asicdruide/CMPG/Portal/1x_5mm_Portal-motor_spacer.dxf

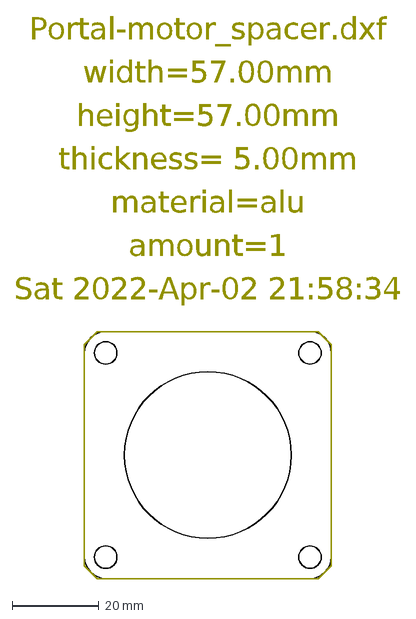
[picture p15: CAD file, 2022-04-06]
Portal/1x_5mm_Portal-motor_spacer.dxf
Portal-motor_spacer.dxf
width=57.00mm
height=57.00mm
thickness= 5.00mm
material=alu
amount=1
Sat 2022-Apr-02 21:58:34
