asicdruide/CMPG/Z-Axis/1x_15mm_Z-Axis-top.dxf

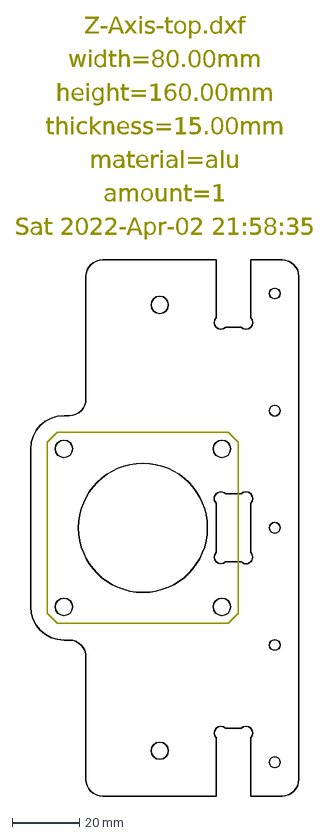
[picture p16: CAD file, 2022-04-06]
Z-Axis/1x_15mm_Z-Axis-top.dxf
Z-Axis-top.dxf
width=80.00mm
height=160.00mm
thickness=15.00mm
material=alu
amount=1
Sat 2022-Apr-02 21:58:35
