asicdruide/CMPG/Frame/1x_10mm_Frame-back-left.dxf

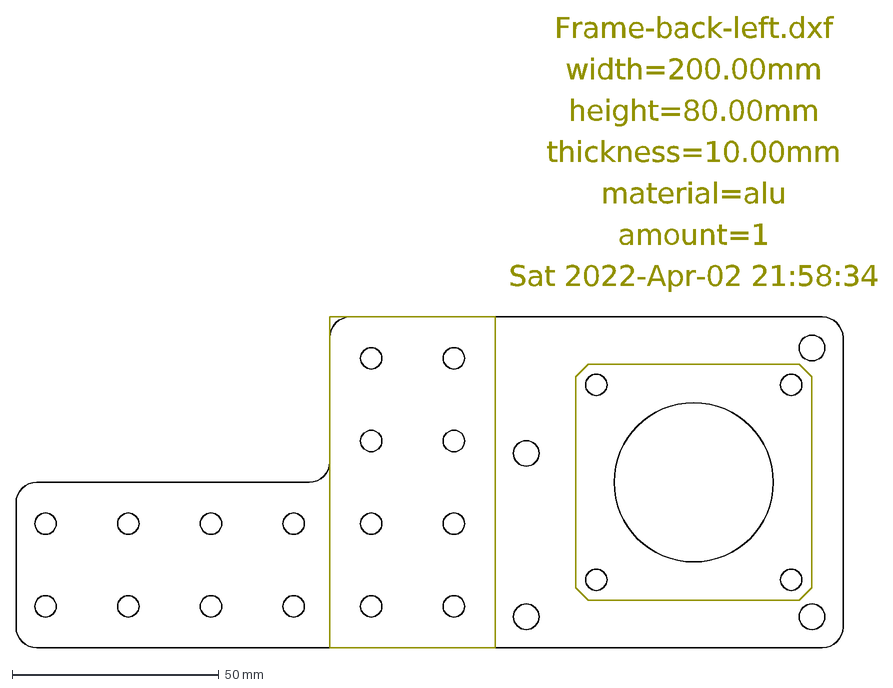
[picture p17: CAD file, 2022-04-06]
Frame/1x_10mm_Frame-back-left.dxf
Frame-back-left.dxf
width=200.00mm
height=80.00mm
thickness=10.00mm
material=alu
amount=1
Sat 2022-Apr-02 21:58:34
