asicdruide/CMPG/generated/1x_5mm_Portal-motor_spacer.dxf

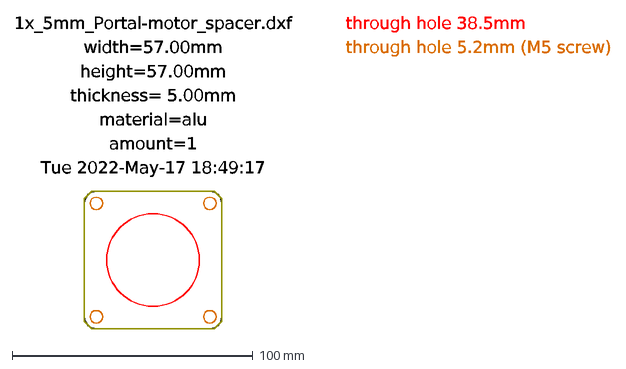
[picture p18: CAD file, 2022-05-19]
generated/1x_5mm_Portal-motor_spacer.dxf
1x_5mm_Portal-motor_spacer.dxf
width=57.00mm
height=57.00mm
thickness= 5.00mm
material=alu
amount=1
Tue 2022-May-17 18:49:17
through hole 38.5mm
through hole 5.2mm (M5 screw)
