asicdruide/CMPG/Z-Axis/1x_10mm_Z-Axis-spindle-AM_1.5kW_ER11.dxf

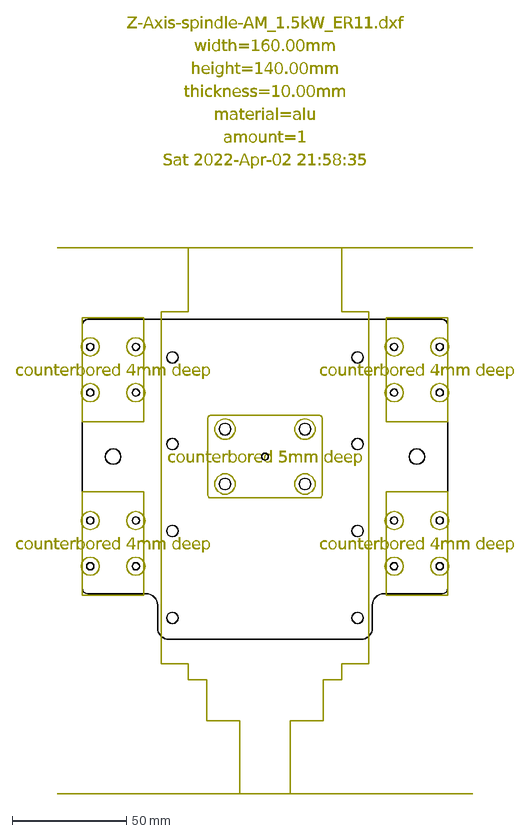
[picture p19: CAD file, 2022-04-06]
Z-Axis/1x_10mm_Z-Axis-spindle-AM_1.5kW_ER11.dxf
counterbored 4mm deep
counterbored 5mm deep
Z-Axis-spindle-AM_1.5kW_ER11.dxf
width=160.00mm
height=140.00mm
thickness=10.00mm
material=alu
amount=1
Sat 2022-Apr-02 21:58:35
