asicdruide/CMPG/generated/1x_10mm_Portal-block.dxf

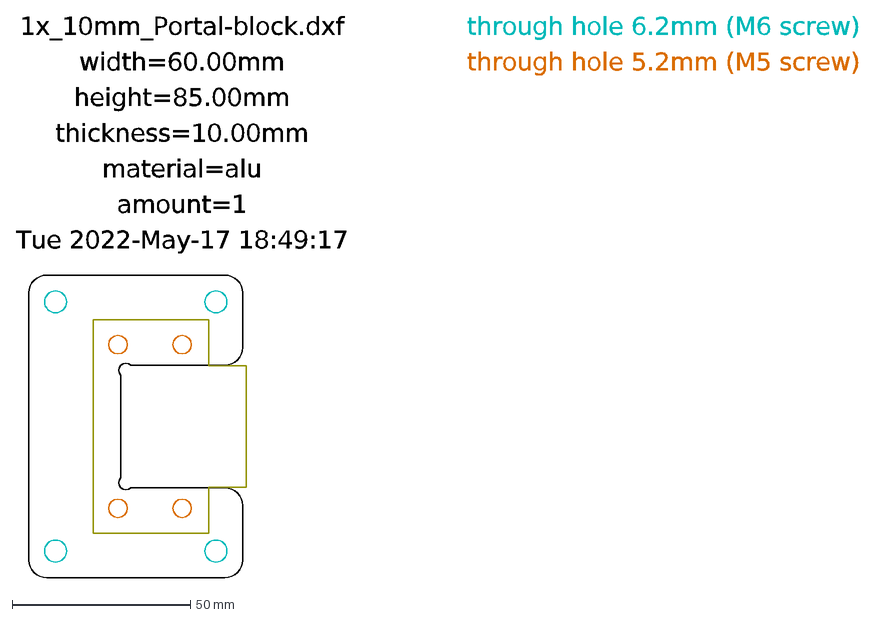
[picture p21: CAD file, 2022-05-19]
generated/1x_10mm_Portal-block.dxf
1x_10mm_Portal-block.dxf
width=60.00mm
height=85.00mm
thickness=10.00mm
material=alu
amount=1
Tue 2022-May-17 18:49:17
through hole 6.2mm (M6 screw)
through hole 5.2mm (M5 screw)
