asicdruide/CMPG/Portal/1x_10mm_Portal-motor_spacer.dxf

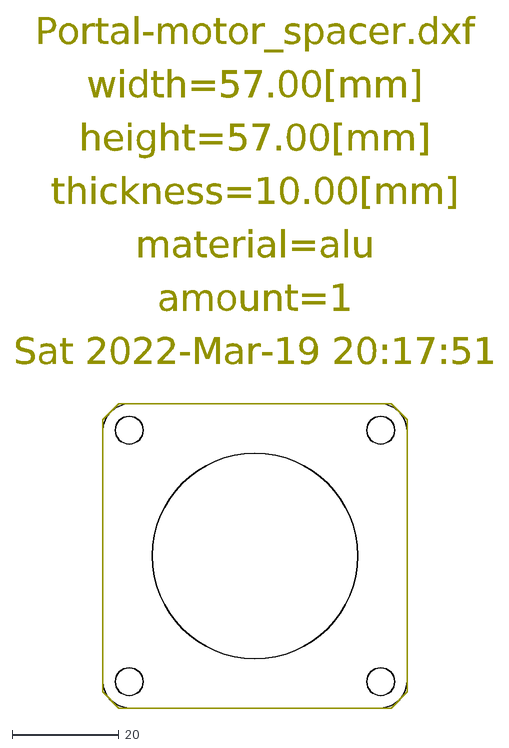
[picture p22: CAD file, 2022-03-19]
Portal/1x_10mm_Portal-motor_spacer.dxf
Portal-motor_spacer.dxf
width=57.00[mm]
height=57.00[mm]
thickness=10.00[mm]
material=alu
amount=1
Sat 2022-Mar-19 20:17:51
