asicdruide/CMPG/Z-Axis/1x_10mm_Z-Axis-back.dxf

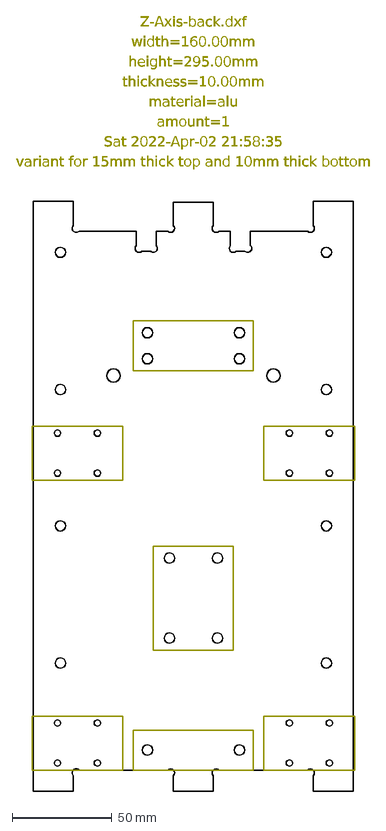
[picture p23: CAD file, 2022-04-06]
Z-Axis/1x_10mm_Z-Axis-back.dxf
Z-Axis-back.dxf
width=160.00mm
height=295.00mm
thickness=10.00mm
material=alu
amount=1
Sat 2022-Apr-02 21:58:35
variant for 15mm thick top and 10mm thick bottom
