asicdruide/CMPG/Frame/1x_10mm_Frame-Plate-back-left.dxf

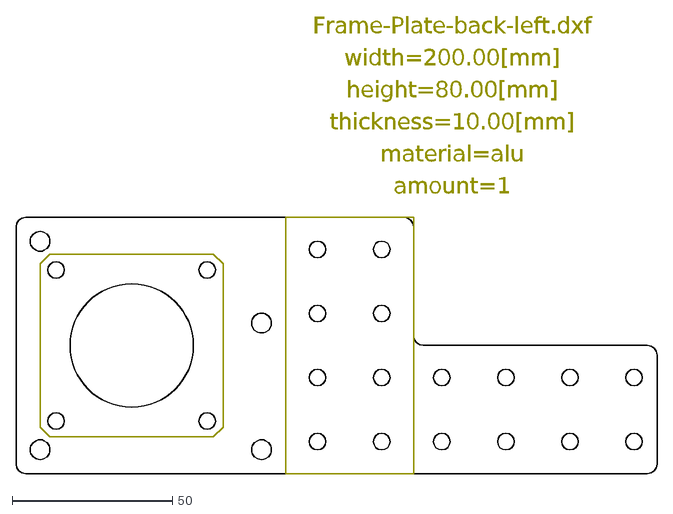
[picture p24: CAD file, 2022-03-18]
Frame/1x_10mm_Frame-Plate-back-left.dxf
Frame-Plate-back-left.dxf
width=200.00[mm]
height=80.00[mm]
thickness=10.00[mm]
material=alu
amount=1
