asicdruide/CMPG/generated/1x_10mm_ZAxis-bottom.dxf

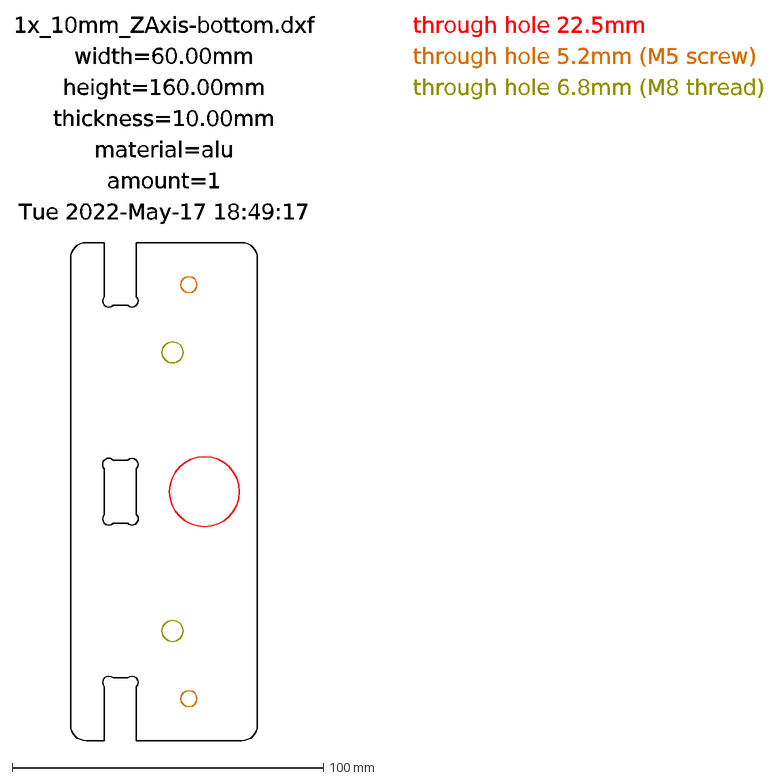
[picture p25: CAD file, 2022-05-19]
generated/1x_10mm_ZAxis-bottom.dxf
1x_10mm_ZAxis-bottom.dxf
width=60.00mm
height=160.00mm
thickness=10.00mm
material=alu
amount=1
Tue 2022-May-17 18:49:17
through hole 22.5mm
through hole 5.2mm (M5 screw)
through hole 6.8mm (M8 thread)
