asicdruide/CMPG/Portal/2x_5mm_Portal-side_plate_spacer.dxf

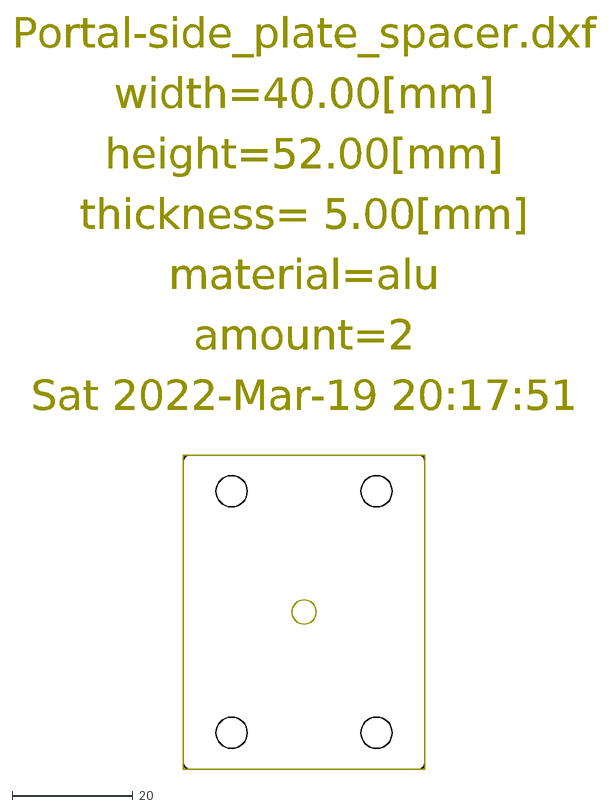
[picture p26: CAD file, 2022-03-19]
Portal/2x_5mm_Portal-side_plate_spacer.dxf
Portal-side_plate_spacer.dxf
width=40.00[mm]
height=52.00[mm]
thickness= 5.00[mm]
material=alu
amount=2
Sat 2022-Mar-19 20:17:51
