asicdruide/CMPG/Portal/1x_10mm_Portal-side-left.dxf

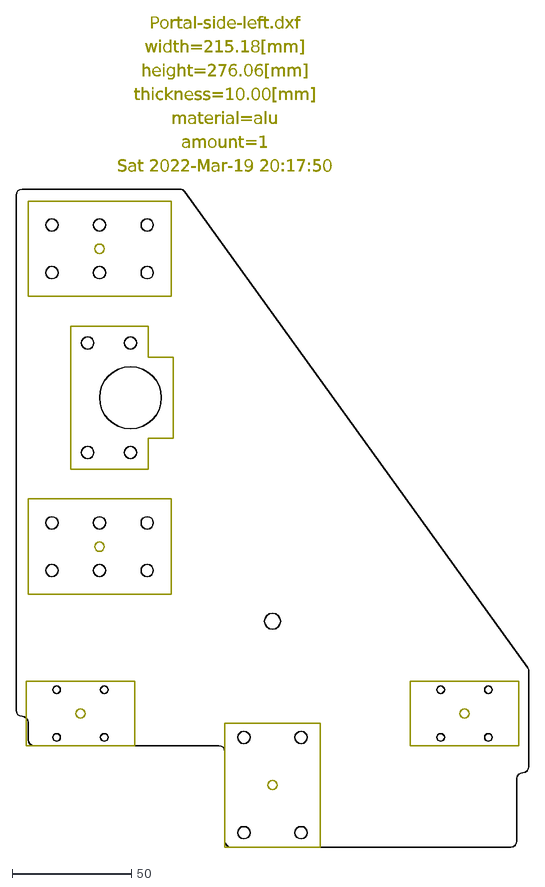
[picture p30: CAD file, 2022-03-19]
Portal/1x_10mm_Portal-side-left.dxf
Portal-side-left.dxf
width=215.18[mm]
height=276.06[mm]
thickness=10.00[mm]
material=alu
amount=1
Sat 2022-Mar-19 20:17:50
