asicdruide/CMPG/Z-Axis/1x_10mm_Z-Axis-spindle-GP_2.2kW_ER20.dxf

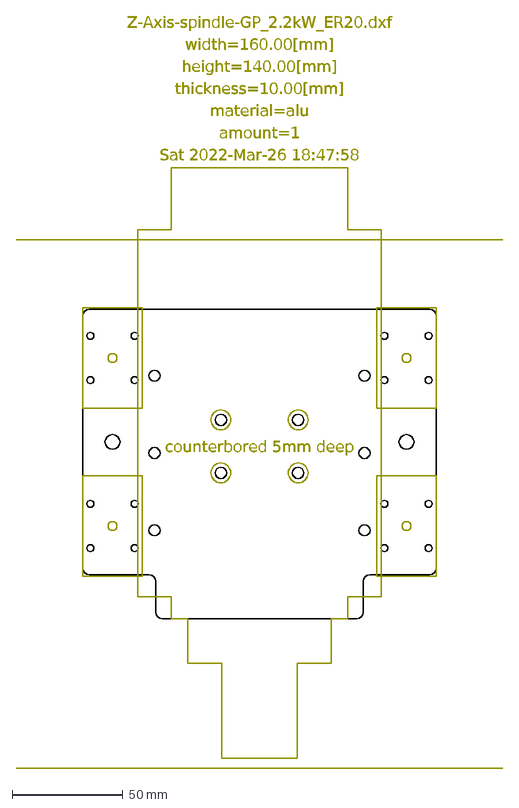
[picture p31: CAD file, 2022-03-27]
Z-Axis/1x_10mm_Z-Axis-spindle-GP_2.2kW_ER20.dxf
counterbored 5mm deep
Z-Axis-spindle-GP_2.2kW_ER20.dxf
width=160.00[mm]
height=140.00[mm]
thickness=10.00[mm]
material=alu
amount=1
Sat 2022-Mar-26 18:47:58
