asicdruide/CMPG/Frame/1x_10mm_Frame-Plate-block-right.dxf

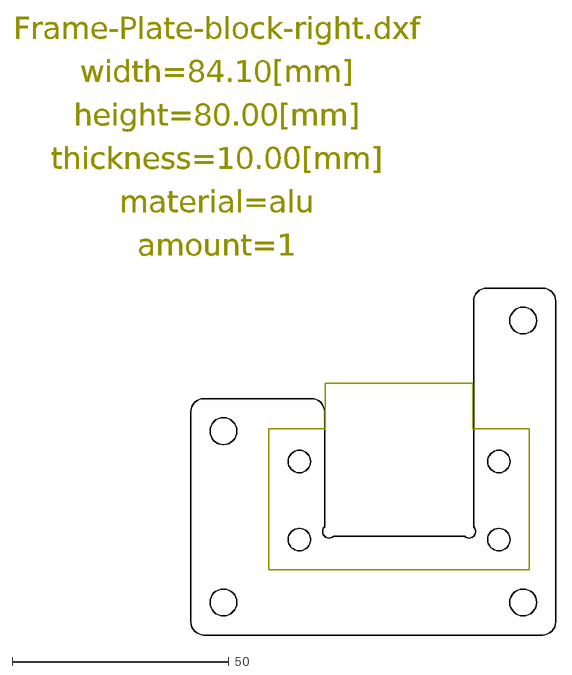
[picture p32: CAD file, 2022-03-18]
Frame/1x_10mm_Frame-Plate-block-right.dxf
Frame-Plate-block-right.dxf
width=84.10[mm]
height=80.00[mm]
thickness=10.00[mm]
material=alu
amount=1
