asicdruide/CMPG/generated/1x_10mm_Frame-front-left.dxf

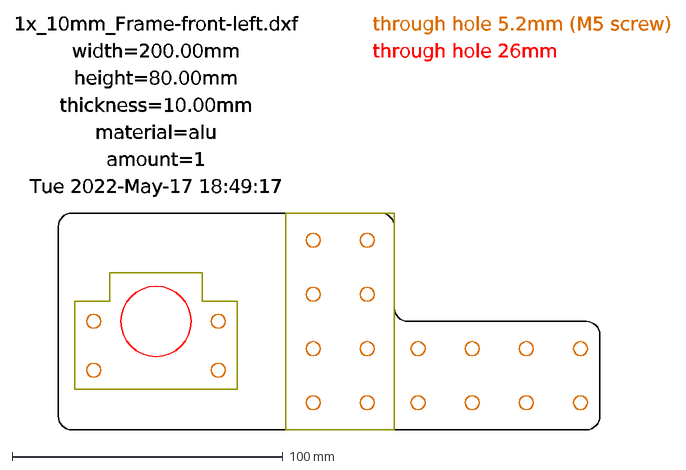
[picture p33: CAD file, 2022-05-19]
generated/1x_10mm_Frame-front-left.dxf
1x_10mm_Frame-front-left.dxf
width=200.00mm
height=80.00mm
thickness=10.00mm
material=alu
amount=1
Tue 2022-May-17 18:49:17
through hole 5.2mm (M5 screw)
through hole 26mm
