asicdruide/CMPG/Z-Axis/1x_5mm_Z-Axis-motor_spacer.dxf

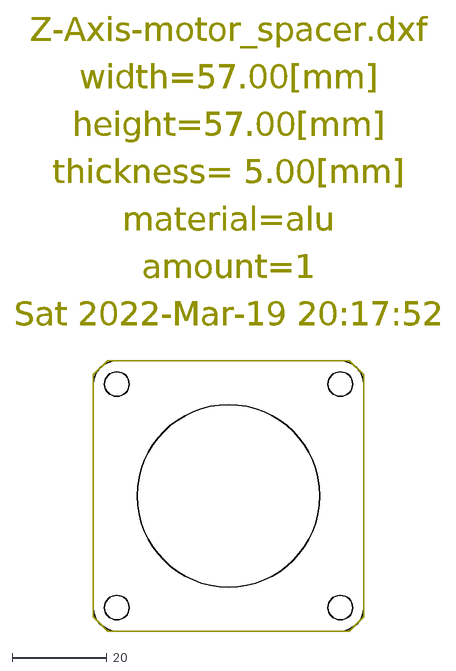
[picture p35: CAD file, 2022-03-19]
Z-Axis/1x_5mm_Z-Axis-motor_spacer.dxf
Z-Axis-motor_spacer.dxf
width=57.00[mm]
height=57.00[mm]
thickness= 5.00[mm]
material=alu
amount=1
Sat 2022-Mar-19 20:17:52
