asicdruide/CMPG/Frame/1x_10mm_Frame-Plate-back-right.dxf

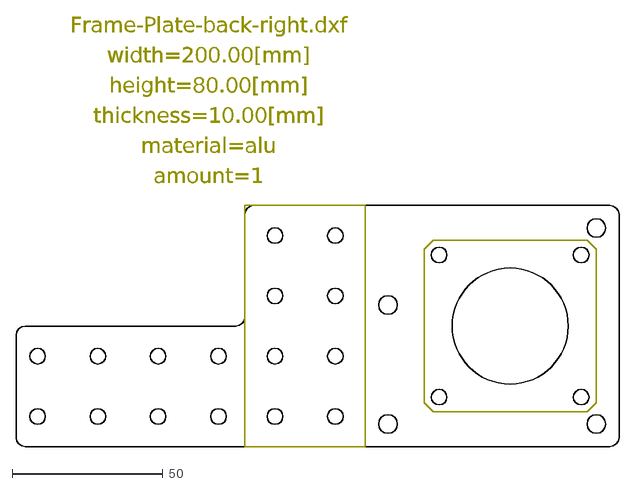
[picture p36: CAD file, 2022-03-18]
Frame/1x_10mm_Frame-Plate-back-right.dxf
Frame-Plate-back-right.dxf
width=200.00[mm]
height=80.00[mm]
thickness=10.00[mm]
material=alu
amount=1
