asicdruide/CMPG/Portal/1x_10mm_Portal-Plate-back.dxf

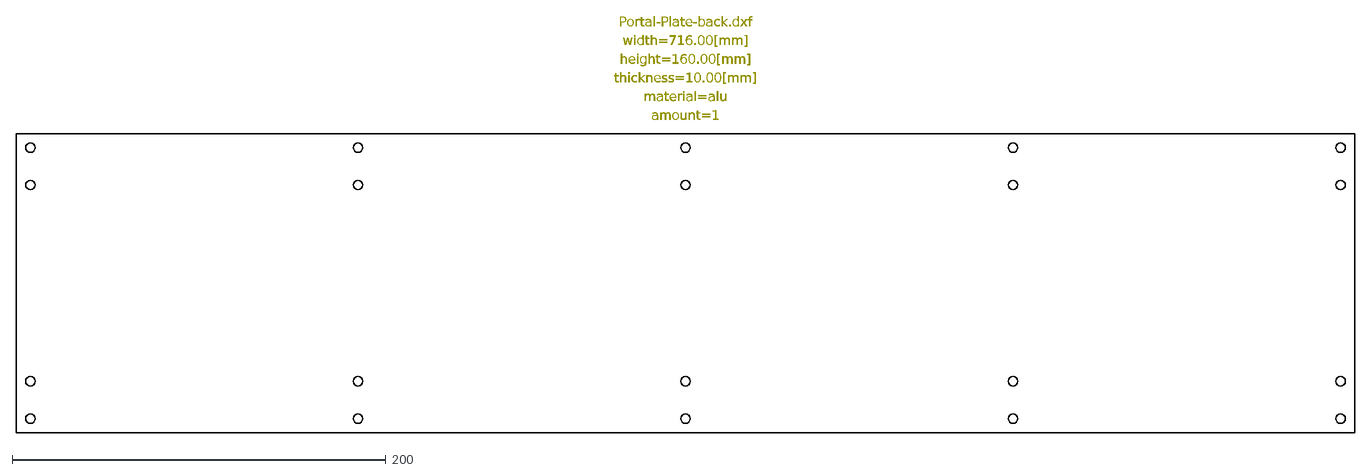
[picture p38: CAD file, 2022-03-18]
Portal/1x_10mm_Portal-Plate-back.dxf
Portal-Plate-back.dxf
width=716.00[mm]
height=160.00[mm]
thickness=10.00[mm]
material=alu
amount=1
