asicdruide/CMPG/Z-Axis/1x_10mm_Z-Axis-top.dxf

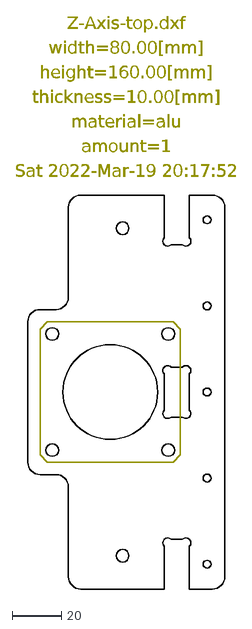
[picture p39: CAD file, 2022-03-19]
Z-Axis/1x_10mm_Z-Axis-top.dxf
Z-Axis-top.dxf
width=80.00[mm]
height=160.00[mm]
thickness=10.00[mm]
material=alu
amount=1
Sat 2022-Mar-19 20:17:52
