asicdruide/CMPG/Frame/1x_10mm_Frame-Plate-block-left.dxf

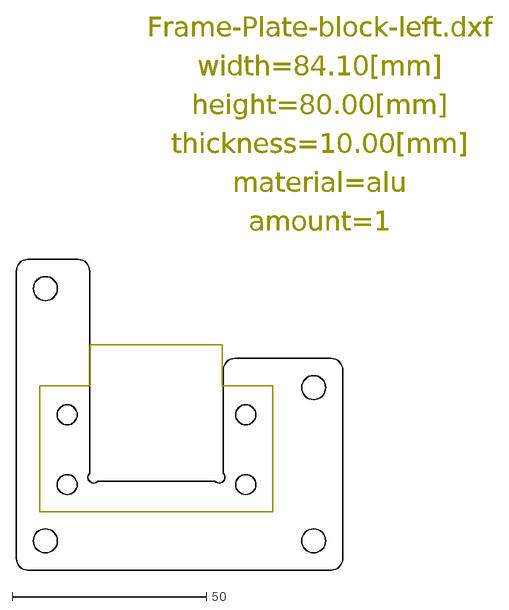
[picture p40: CAD file, 2022-03-18]
Frame/1x_10mm_Frame-Plate-block-left.dxf
Frame-Plate-block-left.dxf
width=84.10[mm]
height=80.00[mm]
thickness=10.00[mm]
material=alu
amount=1
