asicdruide/CMPG/generated/1x_15mm_Portal-side-left.dxf

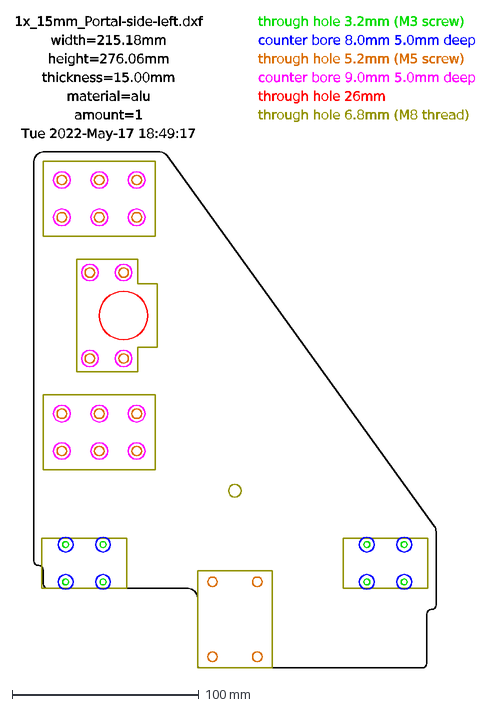
[picture p41: CAD file, 2022-05-19]
generated/1x_15mm_Portal-side-left.dxf
1x_15mm_Portal-side-left.dxf
width=215.18mm
height=276.06mm
thickness=15.00mm
material=alu
amount=1
Tue 2022-May-17 18:49:17
through hole 3.2mm (M3 screw)
counter bore 8.0mm 5.0mm deep
through hole 5.2mm (M5 screw)
counter bore 9.0mm 5.0mm deep
through hole 26mm
through hole 6.8mm (M8 thread)
