asicdruide/CMPG/Z-Axis/1x_10mm_Z-Axis-Plate-bottom.dxf

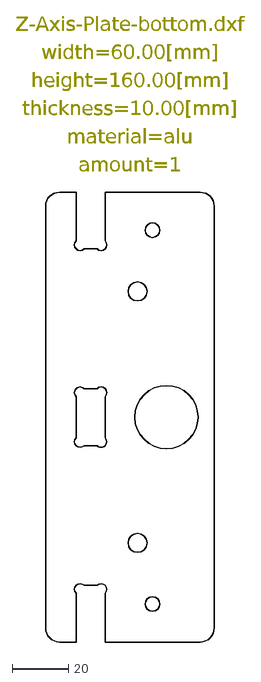
[picture p43: CAD file, 2022-03-18]
Z-Axis/1x_10mm_Z-Axis-Plate-bottom.dxf
Z-Axis-Plate-bottom.dxf
width=60.00[mm]
height=160.00[mm]
thickness=10.00[mm]
material=alu
amount=1
