asicdruide/CMPG/Frame/1x_10mm_Frame-Plate-front-left.dxf

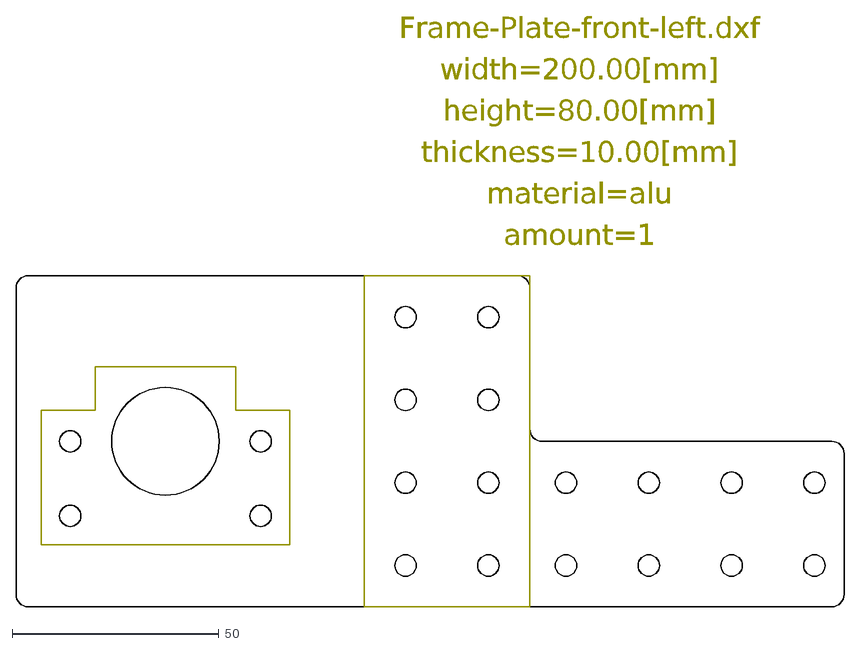
[picture p44: CAD file, 2022-03-18]
Frame/1x_10mm_Frame-Plate-front-left.dxf
Frame-Plate-front-left.dxf
width=200.00[mm]
height=80.00[mm]
thickness=10.00[mm]
material=alu
amount=1
