asicdruide/CMPG/generated/1x_15mm_ZAxis-top.dxf

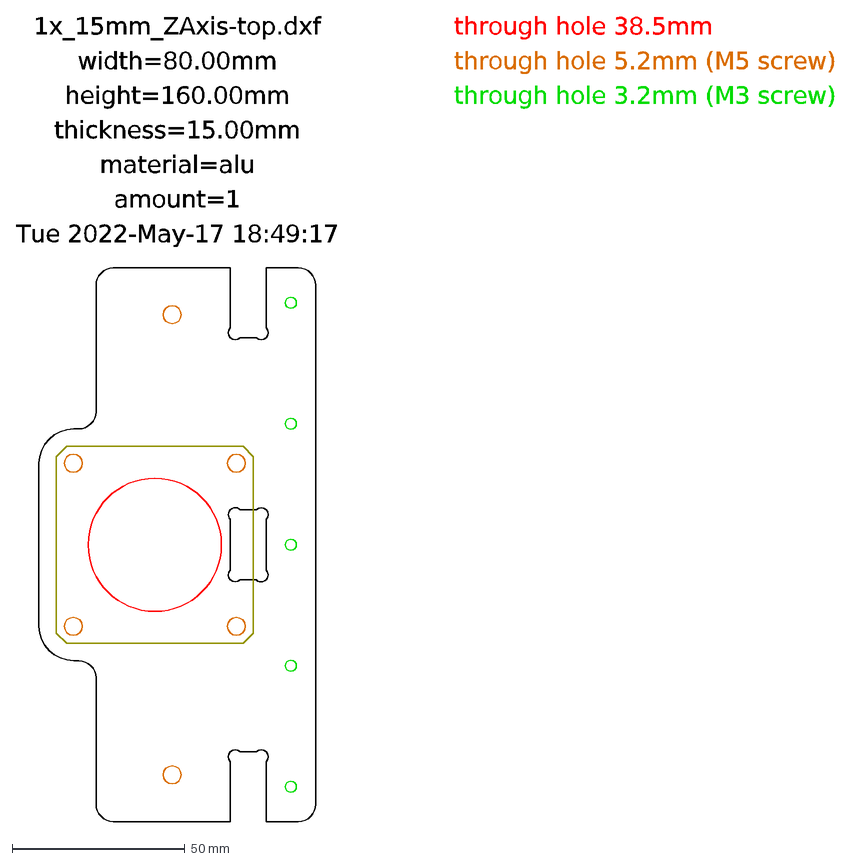
[picture p45: CAD file, 2022-05-19]
generated/1x_15mm_ZAxis-top.dxf
1x_15mm_ZAxis-top.dxf
width=80.00mm
height=160.00mm
thickness=15.00mm
material=alu
amount=1
Tue 2022-May-17 18:49:17
through hole 38.5mm
through hole 5.2mm (M5 screw)
through hole 3.2mm (M3 screw)
