asicdruide/CMPG/Portal/1x_10mm_Portal-Plate-side-right.dxf

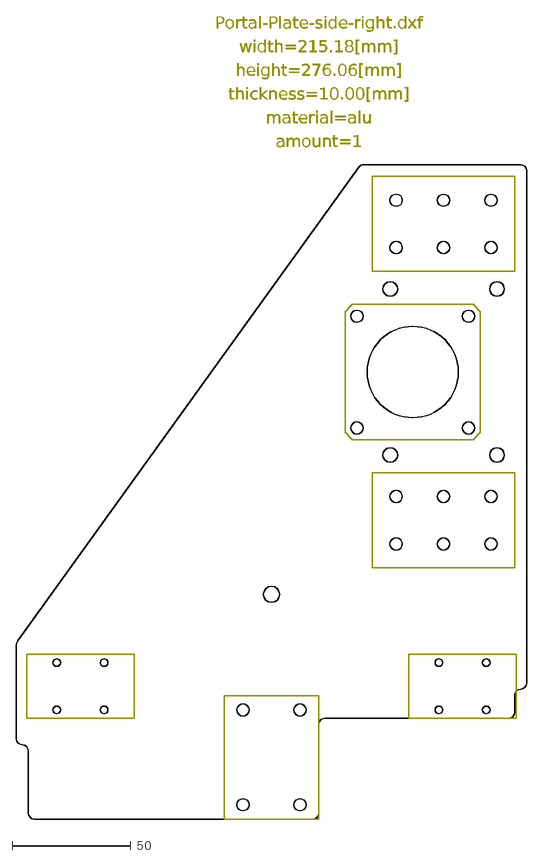
[picture p46: CAD file, 2022-03-18]
Portal/1x_10mm_Portal-Plate-side-right.dxf
Portal-Plate-side-right.dxf
width=215.18[mm]
height=276.06[mm]
thickness=10.00[mm]
material=alu
amount=1
