asicdruide/CMPG/Frame/Frame-Plate-front-right.dxf

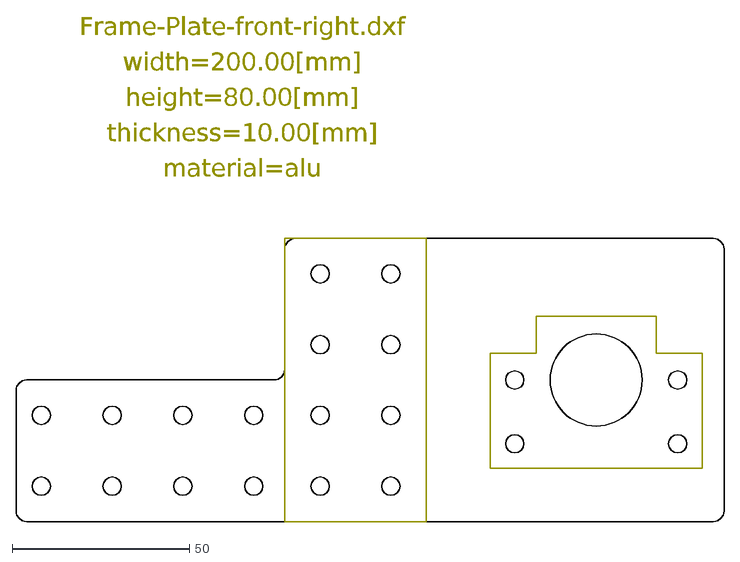
[picture p48: CAD file, 2022-03-16]
Frame/Frame-Plate-front-right.dxf
Frame-Plate-front-right.dxf
width=200.00[mm]
height=80.00[mm]
thickness=10.00[mm]
material=alu
