asicdruide/CMPG/generated/1x_10mm_Frame-back-right.dxf

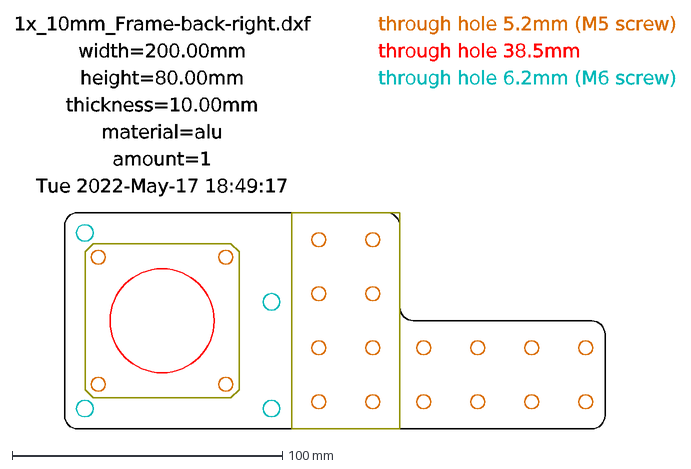
[picture p49: CAD file, 2022-05-19]
generated/1x_10mm_Frame-back-right.dxf
1x_10mm_Frame-back-right.dxf
width=200.00mm
height=80.00mm
thickness=10.00mm
material=alu
amount=1
Tue 2022-May-17 18:49:17
through hole 5.2mm (M5 screw)
through hole 38.5mm
through hole 6.2mm (M6 screw)
