asicdruide/CMPG/Portal/1x_10mm_Portal-Plate-block.dxf

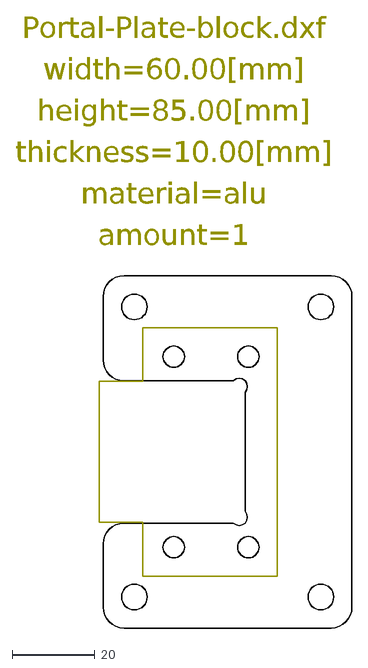
[picture p50: CAD file, 2022-03-18]
Portal/1x_10mm_Portal-Plate-block.dxf
Portal-Plate-block.dxf
width=60.00[mm]
height=85.00[mm]
thickness=10.00[mm]
material=alu
amount=1
