asicdruide/CMPG/Z-Axis/1x_10mm_Z-Axis-Spindle-Plate-GP_1.5kW_ER20.dxf

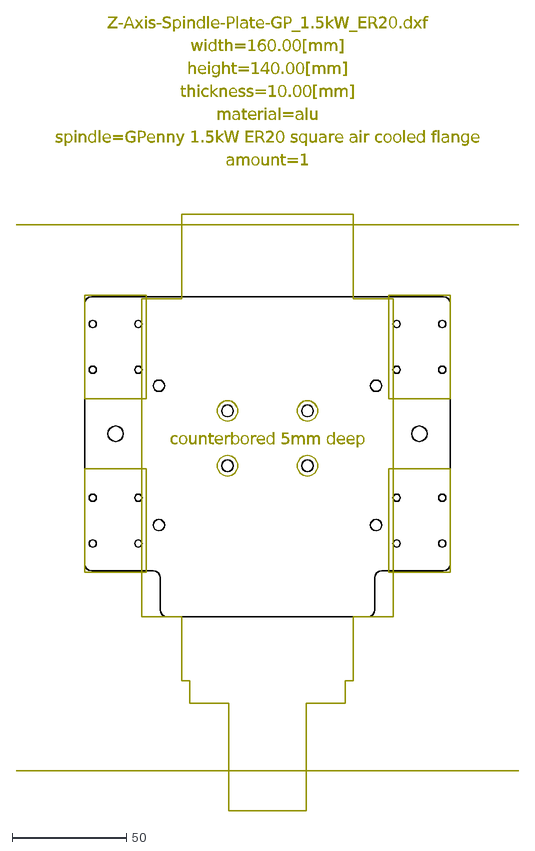
[picture p51: CAD file, 2022-03-18]
Z-Axis/1x_10mm_Z-Axis-Spindle-Plate-GP_1.5kW_ER20.dxf
counterbored 5mm deep
Z-Axis-Spindle-Plate-GP_1.5kW_ER20.dxf
width=160.00[mm]
height=140.00[mm]
thickness=10.00[mm]
material=alu
spindle=GPenny 1.5kW ER20 square air cooled flange
amount=1
