asicdruide/CMPG/Frame/Frame-Plate-back-right.dxf

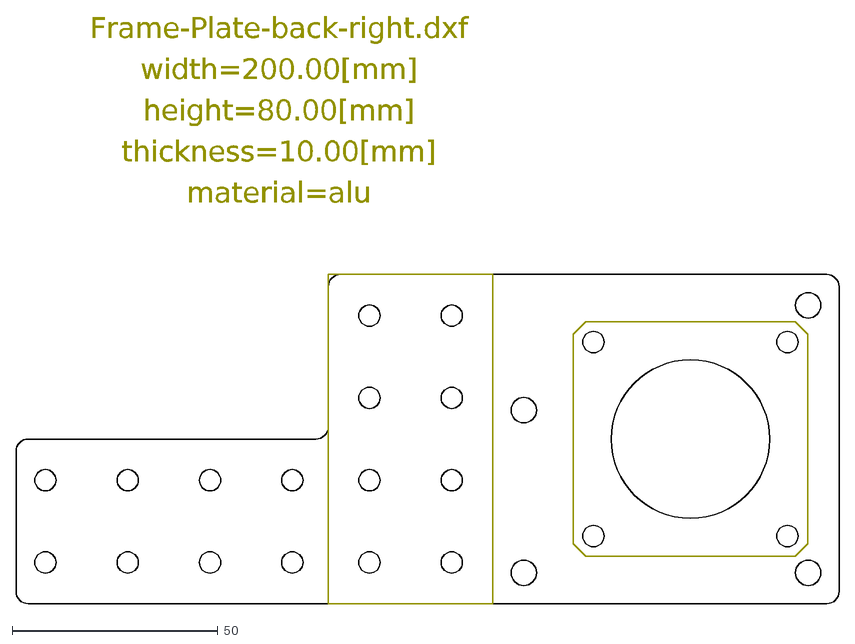
[picture p52: CAD file, 2022-03-16]
Frame/Frame-Plate-back-right.dxf
Frame-Plate-back-right.dxf
width=200.00[mm]
height=80.00[mm]
thickness=10.00[mm]
material=alu
