asicdruide/CMPG/Z-Axis/1x_10mm_Z-Axis-Spindle-Plate-AM_1.5kW_ER11.dxf

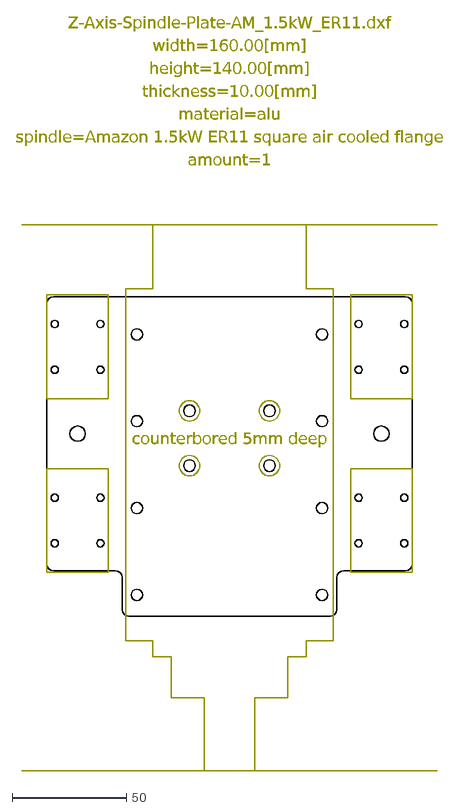
[picture p54: CAD file, 2022-03-18]
Z-Axis/1x_10mm_Z-Axis-Spindle-Plate-AM_1.5kW_ER11.dxf
counterbored 5mm deep
Z-Axis-Spindle-Plate-AM_1.5kW_ER11.dxf
width=160.00[mm]
height=140.00[mm]
thickness=10.00[mm]
material=alu
spindle=Amazon 1.5kW ER11 square air cooled flange
amount=1
