asicdruide/CMPG/Frame/Frame-Plate-front-left.dxf

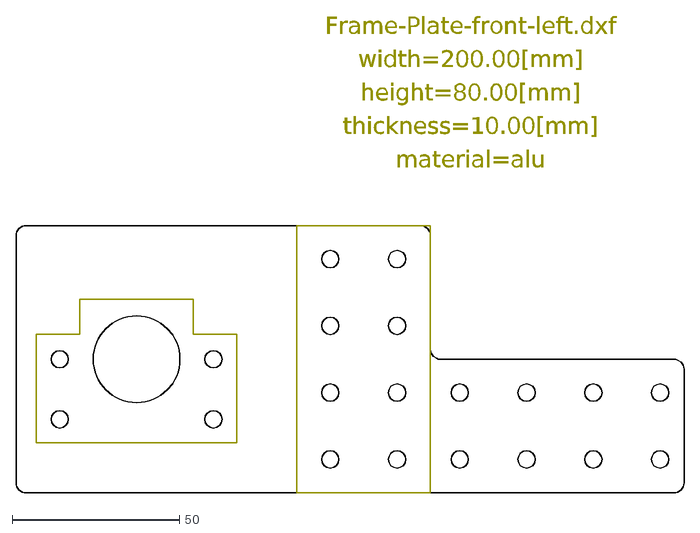
[picture p55: CAD file, 2022-03-16]
Frame/Frame-Plate-front-left.dxf
Frame-Plate-front-left.dxf
width=200.00[mm]
height=80.00[mm]
thickness=10.00[mm]
material=alu
