asicdruide/CMPG/Portal/1x_10mm_Portal-Plate-motor_spacer.dxf

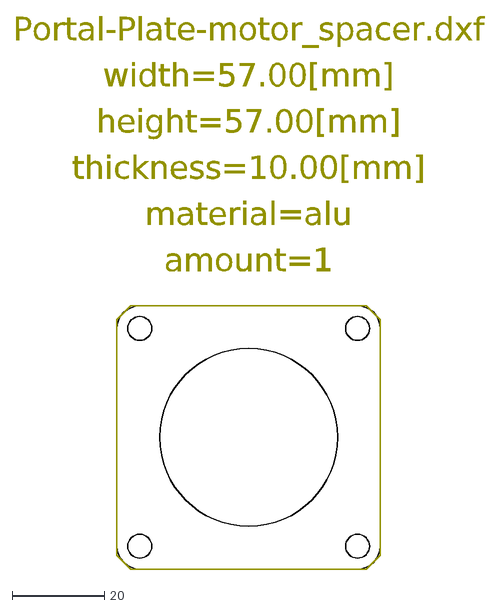
[picture p56: CAD file, 2022-03-18]
Portal/1x_10mm_Portal-Plate-motor_spacer.dxf
Portal-Plate-motor_spacer.dxf
width=57.00[mm]
height=57.00[mm]
thickness=10.00[mm]
material=alu
amount=1
