asicdruide/CMPG/Z-Axis/1x_10mm_Z-Axis-Plate-top.dxf

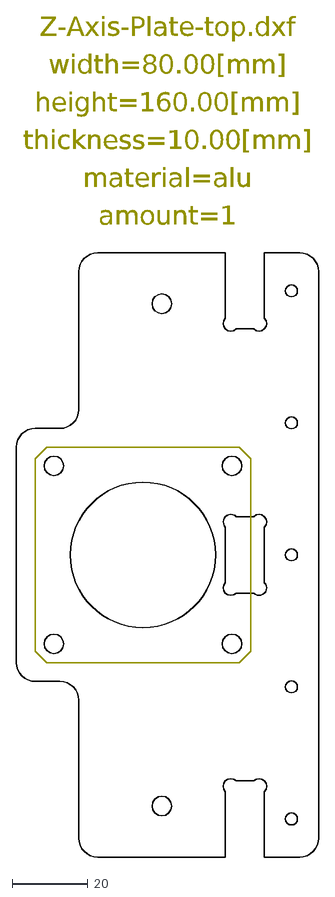
[picture p57: CAD file, 2022-03-18]
Z-Axis/1x_10mm_Z-Axis-Plate-top.dxf
Z-Axis-Plate-top.dxf
width=80.00[mm]
height=160.00[mm]
thickness=10.00[mm]
material=alu
amount=1
