asicdruide/CMPG/Frame/Frame-Plate-block-right.dxf

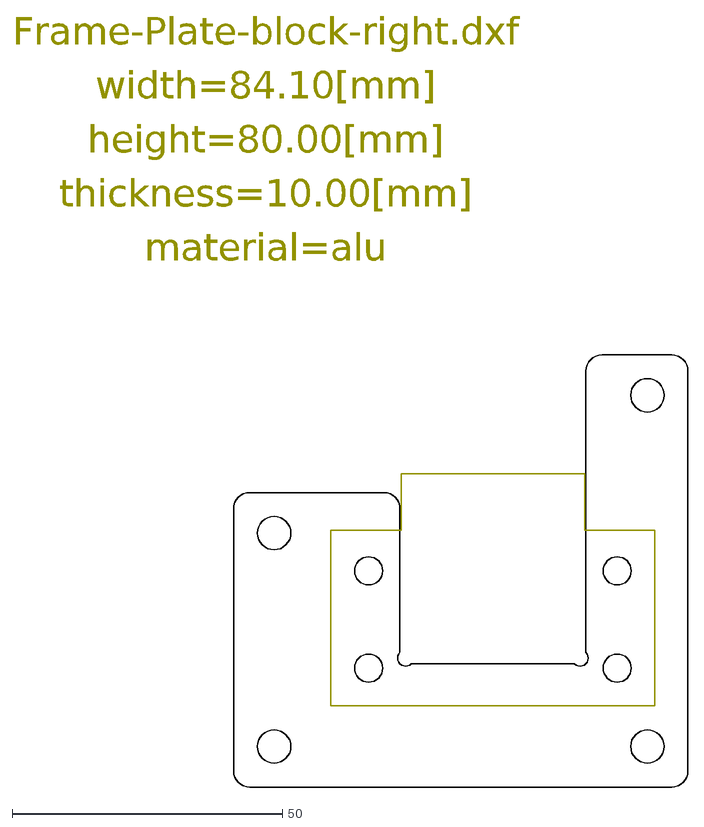
[picture p58: CAD file, 2022-03-16]
Frame/Frame-Plate-block-right.dxf
Frame-Plate-block-right.dxf
width=84.10[mm]
height=80.00[mm]
thickness=10.00[mm]
material=alu
