asicdruide/CMPG/generated/4x_7mm_ZAxis-rail_spacer.dxf

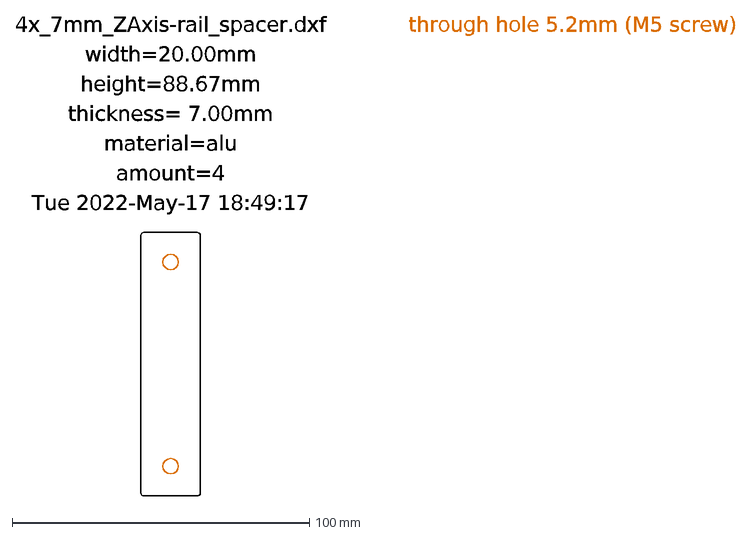
[picture p59: CAD file, 2022-05-19]
generated/4x_7mm_ZAxis-rail_spacer.dxf
4x_7mm_ZAxis-rail_spacer.dxf
width=20.00mm
height=88.67mm
thickness= 7.00mm
material=alu
amount=4
Tue 2022-May-17 18:49:17
through hole 5.2mm (M5 screw)
