asicdruide/CMPG/Portal/2x_5mm_Portal-Plate-side_plate_spacer.dxf

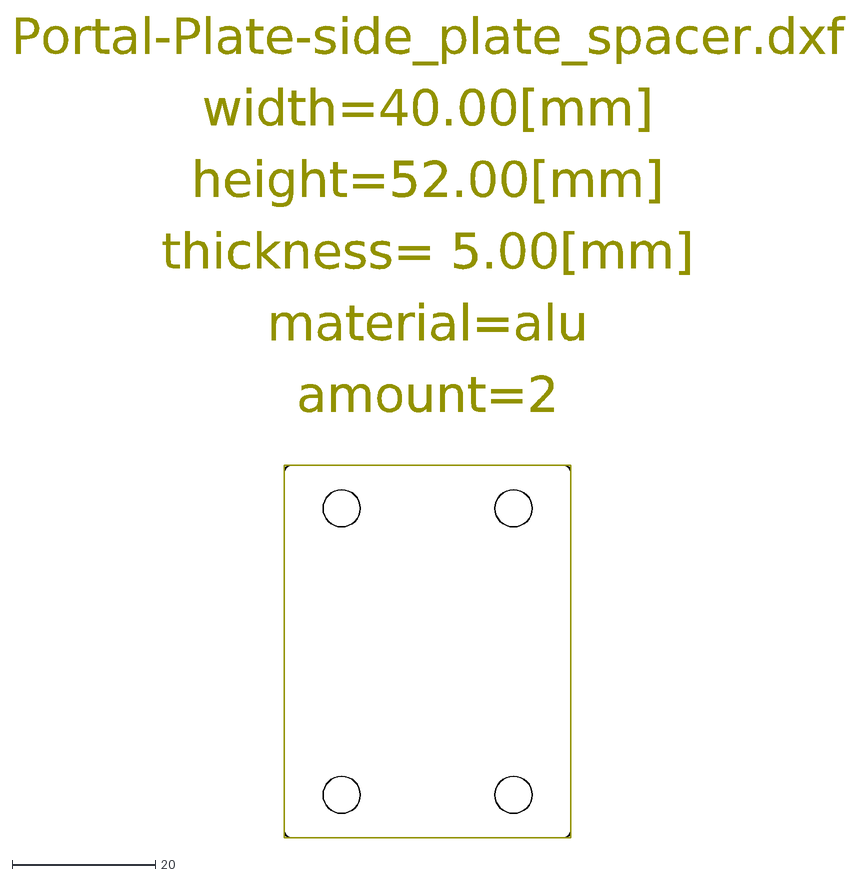
[picture p60: CAD file, 2022-03-18]
Portal/2x_5mm_Portal-Plate-side_plate_spacer.dxf
Portal-Plate-side_plate_spacer.dxf
width=40.00[mm]
height=52.00[mm]
thickness= 5.00[mm]
material=alu
amount=2
