asicdruide/CMPG/Z-Axis/1x_10mm_Z-Axis-Spindle-Plate-GP_2.2kW_ER20.dxf

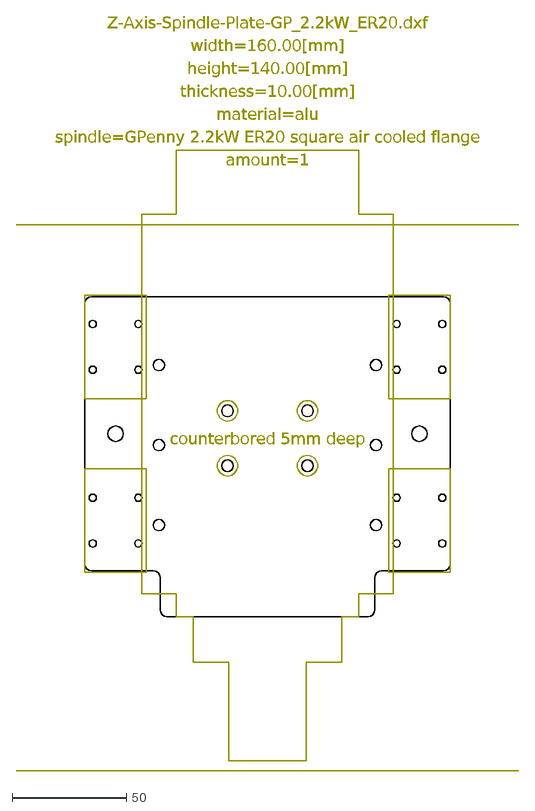
[picture p61: CAD file, 2022-03-18]
Z-Axis/1x_10mm_Z-Axis-Spindle-Plate-GP_2.2kW_ER20.dxf
counterbored 5mm deep
Z-Axis-Spindle-Plate-GP_2.2kW_ER20.dxf
width=160.00[mm]
height=140.00[mm]
thickness=10.00[mm]
material=alu
spindle=GPenny 2.2kW ER20 square air cooled flange
amount=1
