asicdruide/CMPG/Frame/Frame-Plate-back-left.dxf

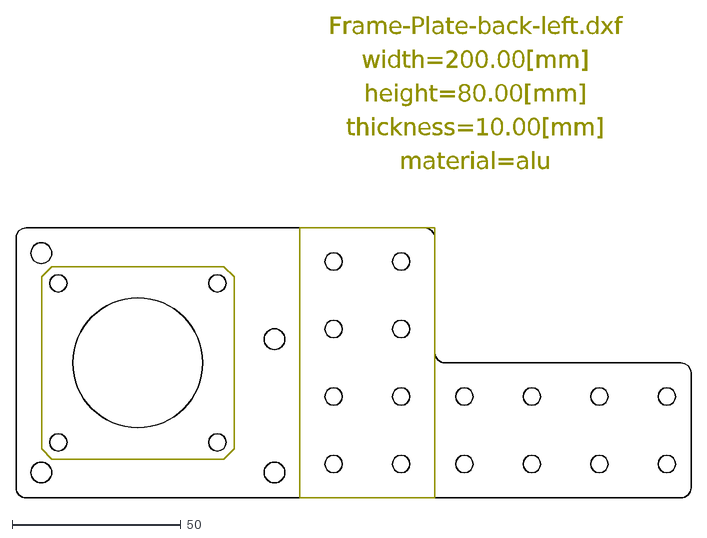
[picture p62: CAD file, 2022-03-16]
Frame/Frame-Plate-back-left.dxf
Frame-Plate-back-left.dxf
width=200.00[mm]
height=80.00[mm]
thickness=10.00[mm]
material=alu
