asicdruide/CMPG/generated/1x_10mm_Portal-back.dxf

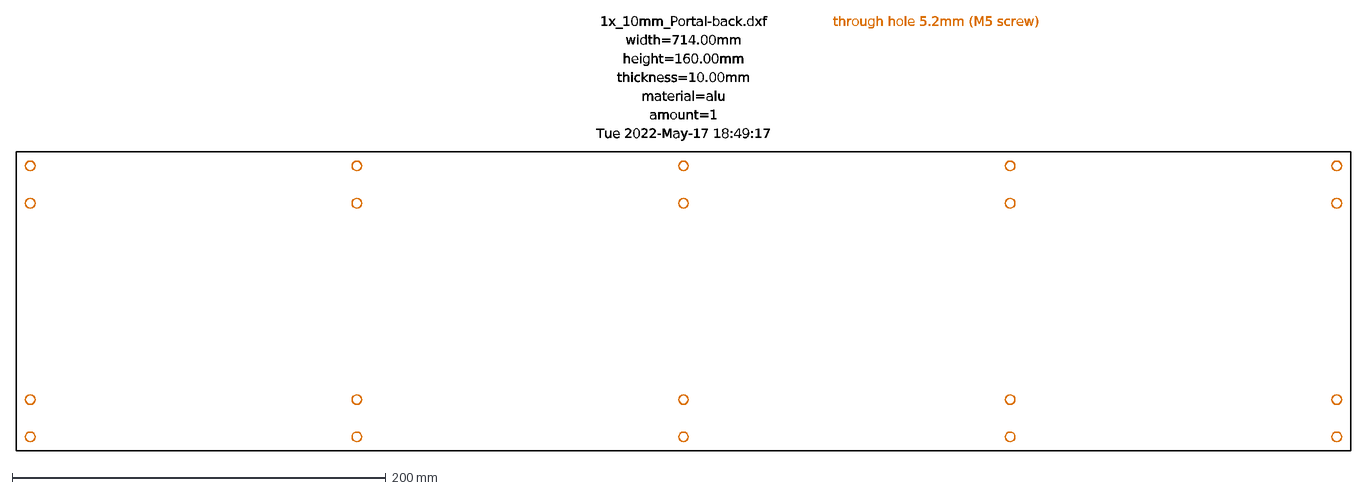
[picture p63: CAD file, 2022-05-19]
generated/1x_10mm_Portal-back.dxf
1x_10mm_Portal-back.dxf
width=714.00mm
height=160.00mm
thickness=10.00mm
material=alu
amount=1
Tue 2022-May-17 18:49:17
through hole 5.2mm (M5 screw)
