asicdruide/CMPG/Portal/Portal-Plate-side_plate_spacer.dxf

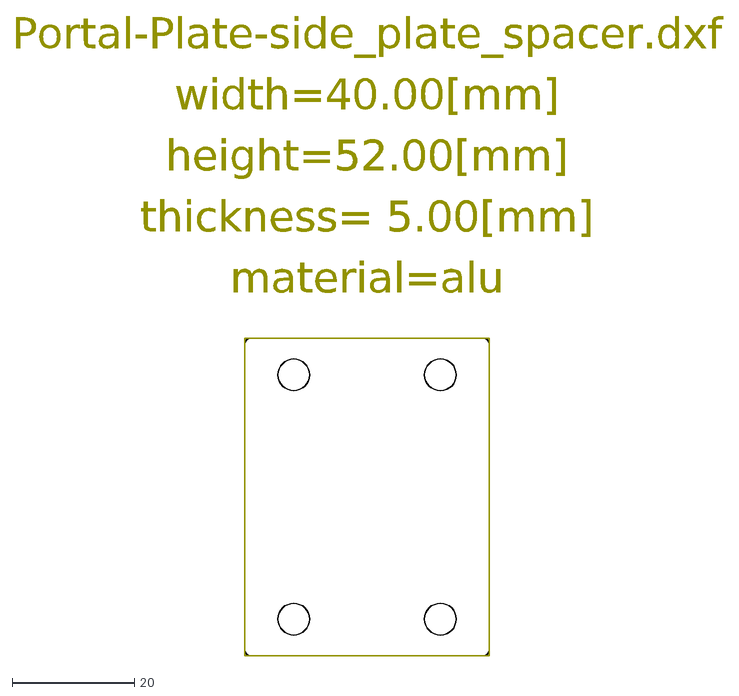
[picture p64: CAD file, 2022-03-17]
Portal/Portal-Plate-side_plate_spacer.dxf
Portal-Plate-side_plate_spacer.dxf
width=40.00[mm]
height=52.00[mm]
thickness= 5.00[mm]
material=alu
