asicdruide/CMPG/Z-Axis/Z-Axis-Plate-top.dxf

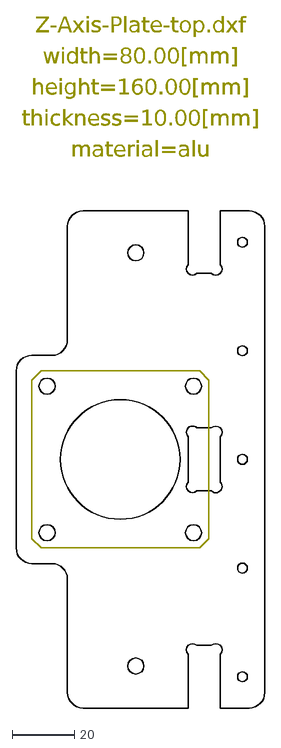
[picture p65: CAD file, 2022-03-17]
Z-Axis/Z-Axis-Plate-top.dxf
Z-Axis-Plate-top.dxf
width=80.00[mm]
height=160.00[mm]
thickness=10.00[mm]
material=alu
