asicdruide/CMPG/Frame/Frame-Plate-block-left.dxf

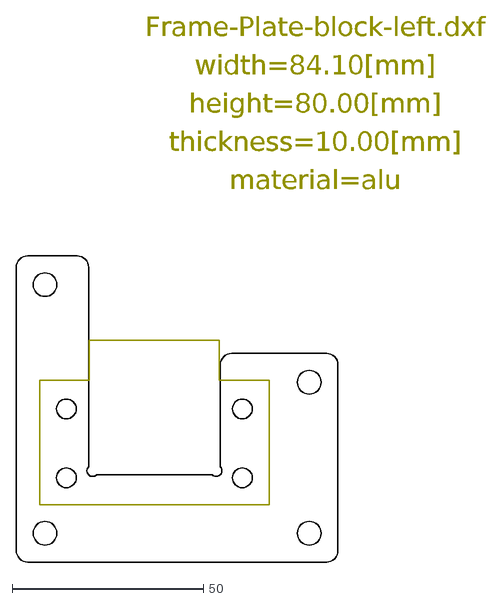
[picture p66: CAD file, 2022-03-16]
Frame/Frame-Plate-block-left.dxf
Frame-Plate-block-left.dxf
width=84.10[mm]
height=80.00[mm]
thickness=10.00[mm]
material=alu
