asicdruide/CMPG/Portal/Portal-Plate-side-left.dxf

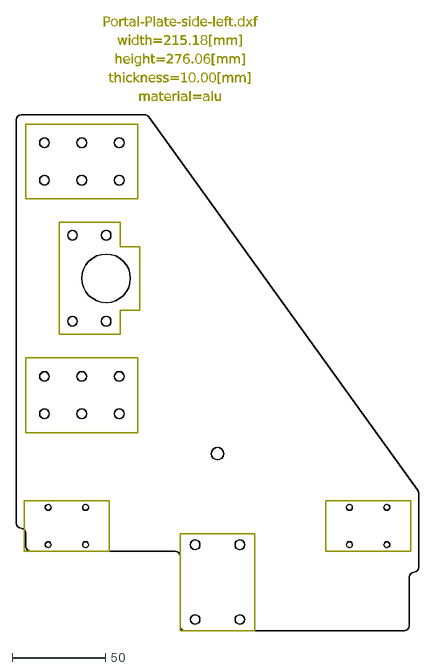
[picture p67: CAD file, 2022-03-17]
Portal/Portal-Plate-side-left.dxf
Portal-Plate-side-left.dxf
width=215.18[mm]
height=276.06[mm]
thickness=10.00[mm]
material=alu
