asicdruide/CMPG/Z-Axis/Z-Axis-Plate-bottom.dxf

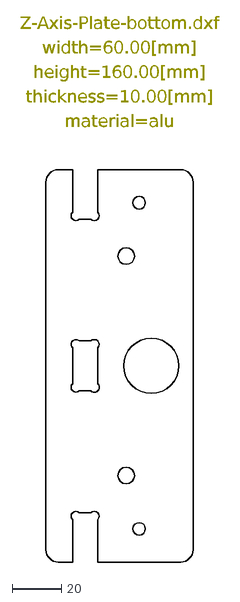
[picture p68: CAD file, 2022-03-17]
Z-Axis/Z-Axis-Plate-bottom.dxf
Z-Axis-Plate-bottom.dxf
width=60.00[mm]
height=160.00[mm]
thickness=10.00[mm]
material=alu
