asicdruide/CMPG/Portal/Portal-Plate-block.dxf

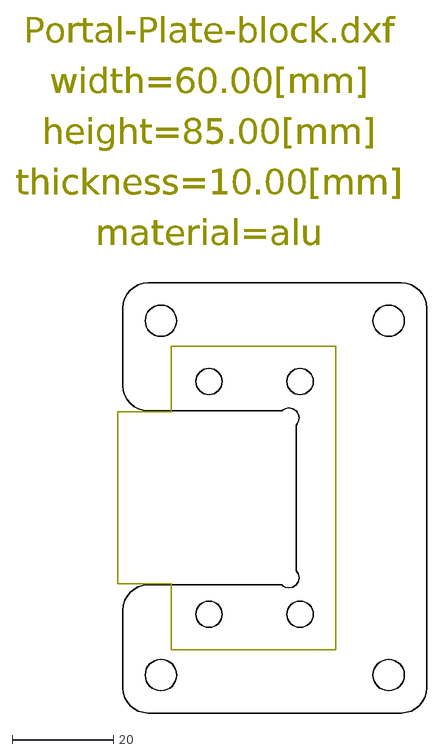
[picture p70: CAD file, 2022-03-17]
Portal/Portal-Plate-block.dxf
Portal-Plate-block.dxf
width=60.00[mm]
height=85.00[mm]
thickness=10.00[mm]
material=alu
