asicdruide/CMPG/Z-Axis/Z-Axis-Spindle-Plate-AM_1.5kW_ER11.dxf

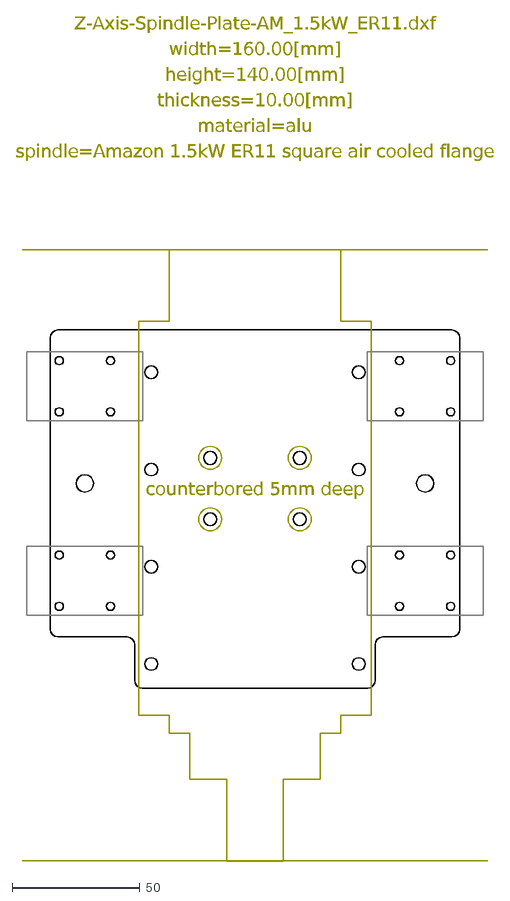
[picture p71: CAD file, 2022-03-16]
Z-Axis/Z-Axis-Spindle-Plate-AM_1.5kW_ER11.dxf
counterbored 5mm deep
Z-Axis-Spindle-Plate-AM_1.5kW_ER11.dxf
width=160.00[mm]
height=140.00[mm]
thickness=10.00[mm]
material=alu
spindle=Amazon 1.5kW ER11 square air cooled flange
