asicdruide/CMPG/Portal/Portal-Plate-motor_spacer.dxf

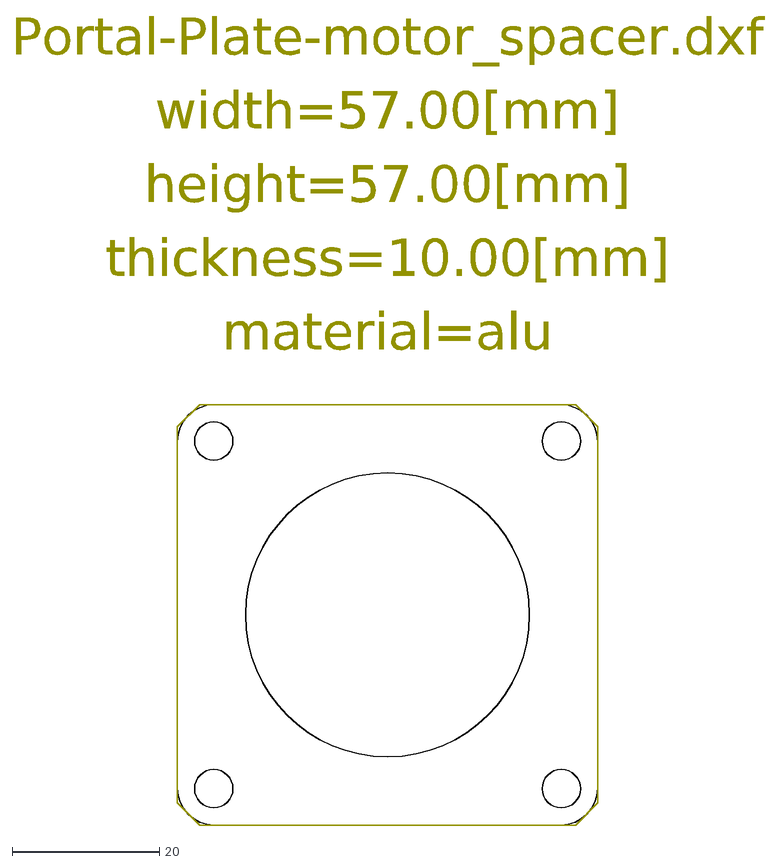
[picture p72: CAD file, 2022-03-17]
Portal/Portal-Plate-motor_spacer.dxf
Portal-Plate-motor_spacer.dxf
width=57.00[mm]
height=57.00[mm]
thickness=10.00[mm]
material=alu
