asicdruide/CMPG/Portal/Portal-Plate-back.dxf

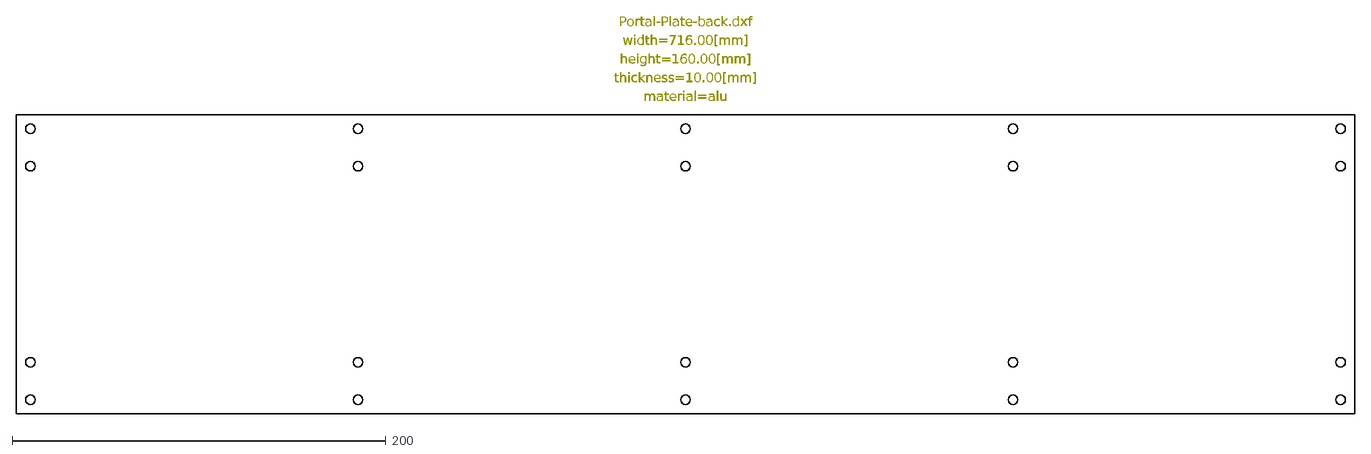
[picture p74: CAD file, 2022-03-17]
Portal/Portal-Plate-back.dxf
Portal-Plate-back.dxf
width=716.00[mm]
height=160.00[mm]
thickness=10.00[mm]
material=alu
