asicdruide/CMPG/Portal/Portal-Plate-side-right.dxf

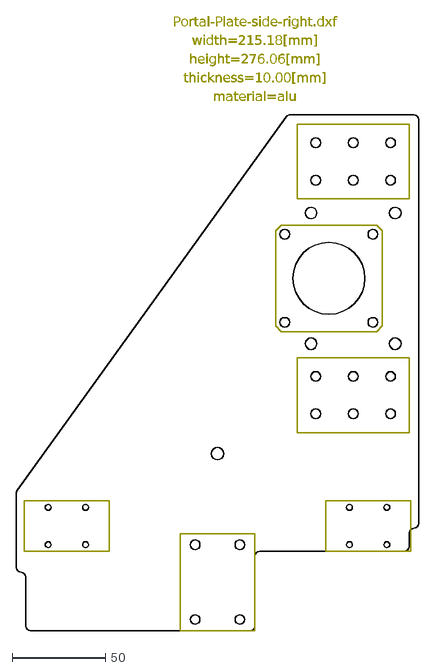
[picture p76: CAD file, 2022-03-16]
Portal/Portal-Plate-side-right.dxf
Portal-Plate-side-right.dxf
width=215.18[mm]
height=276.06[mm]
thickness=10.00[mm]
material=alu
